lsdrckr/tests_and_maintenance/Kicad/PCB_TMS/SparkFun-KiCad-Libraries-main/Capacitor-List.png

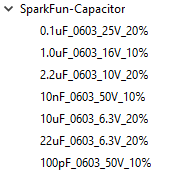
Kicad/PCB_TMS/SparkFun-KiCad-Libraries-main/Capacitor-List.png
