lsdrckr/tests_and_maintenance/Kicad/PCB_TMS/SparkFun-KiCad-Libraries-main/Pre_v7/Documentation/Graphics Work/Symbols_raw.png

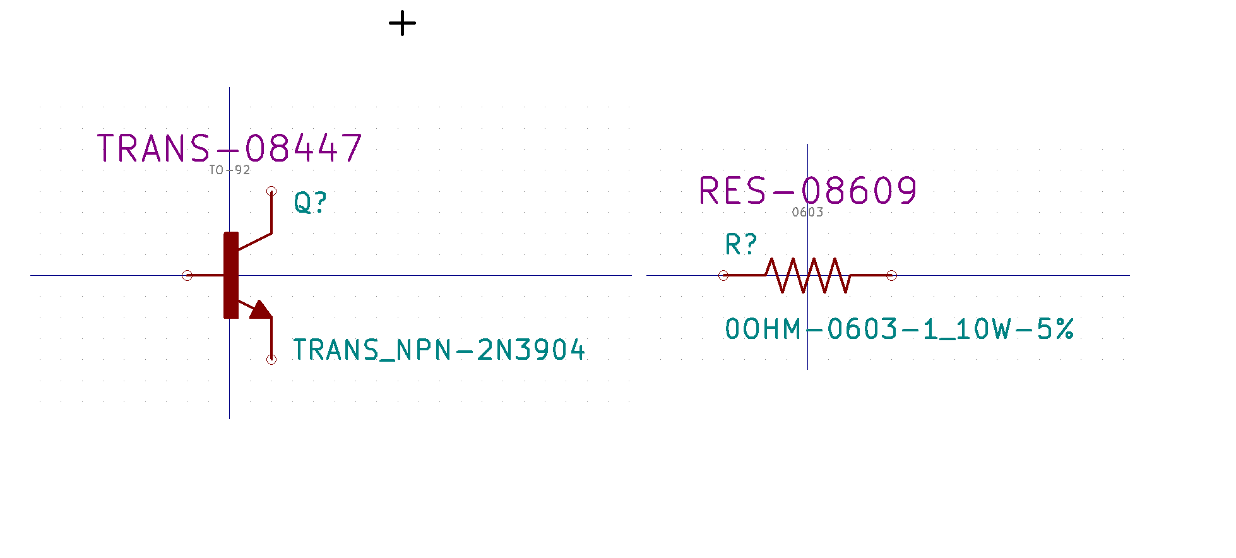
Kicad/PCB_TMS/SparkFun-KiCad-Libraries-main/Pre_v7/Documentation/Graphics Work/Symbols_raw.png
