lsdrckr/tests_and_maintenance/Kicad/PCB_TMS/SparkFun-KiCad-Libraries-main/Pre_v7/Tools/SparkFun-Eagle-Libraries_Conversion/description_tag_example.jpg

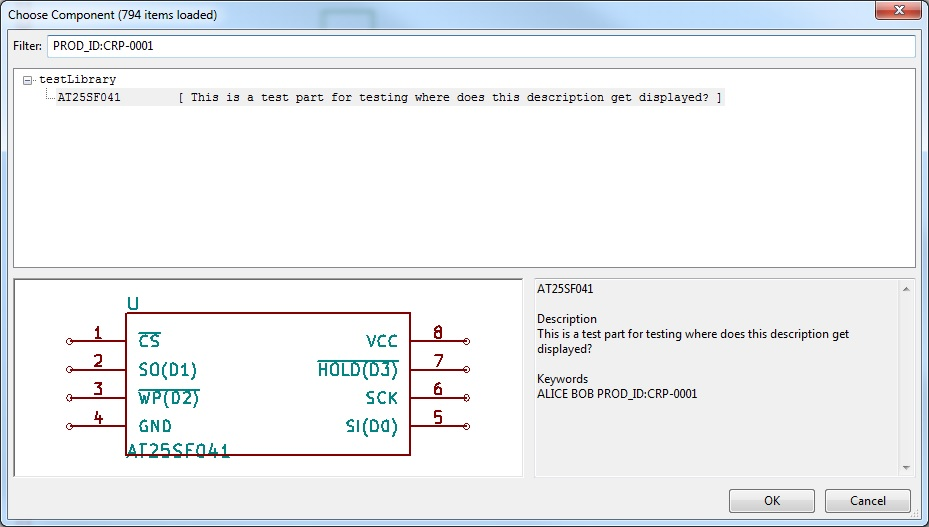
Kicad/PCB_TMS/SparkFun-KiCad-Libraries-main/Pre_v7/Tools/SparkFun-Eagle-Libraries_Conversion/description_tag_example.jpg
