lsdrckr/tests_and_maintenance/Kicad/PCB_TMS/SparkFun-KiCad-Libraries-main/Pre_v7/Tools/SparkFun-Eagle-Libraries_Conversion/example2.jpg

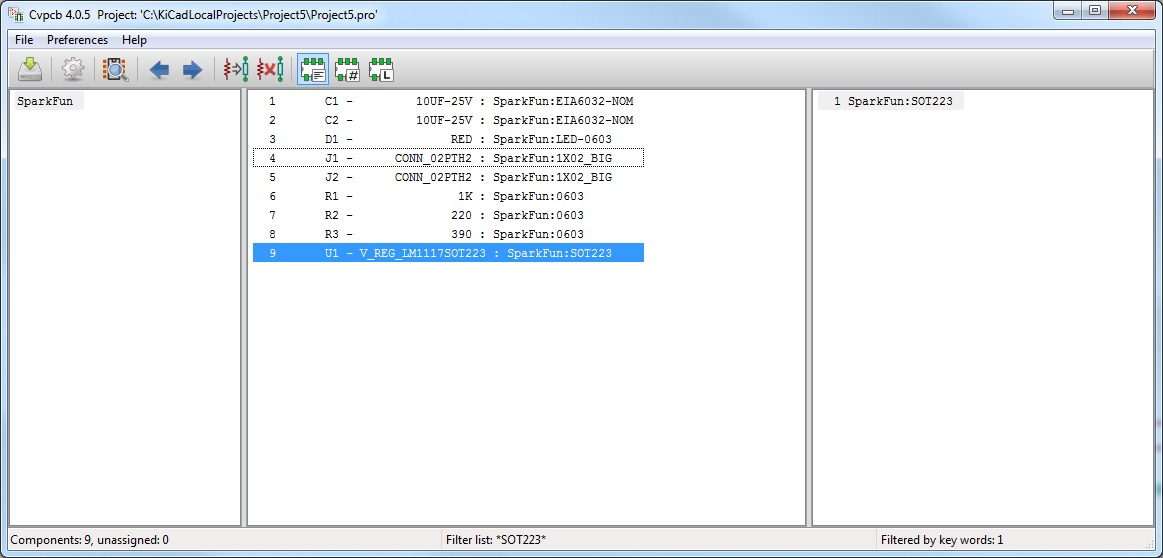
Kicad/PCB_TMS/SparkFun-KiCad-Libraries-main/Pre_v7/Tools/SparkFun-Eagle-Libraries_Conversion/example2.jpg
