lsdrckr/tests_and_maintenance/Kicad/PCB_TMS/SparkFun-KiCad-Libraries-main/Pre_v7/Documentation/Pictures/SymbolGuidelines.png

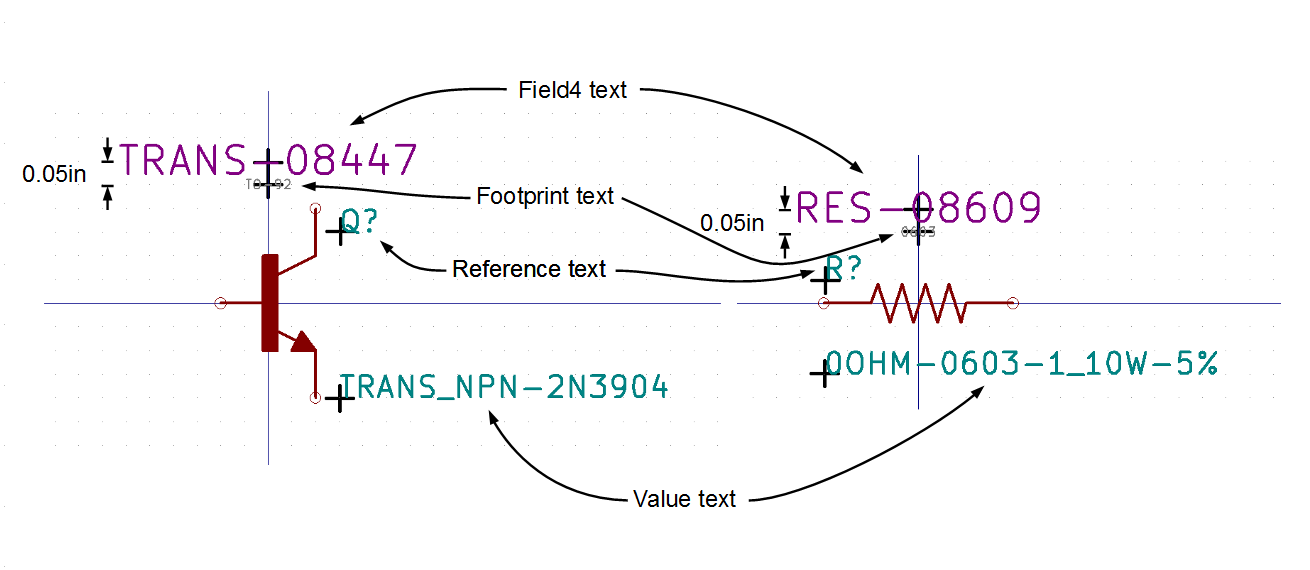
Kicad/PCB_TMS/SparkFun-KiCad-Libraries-main/Pre_v7/Documentation/Pictures/SymbolGuidelines.png
